matosichrvoje/matosic-macropad-pcb/matosic-macropad.kicad_sch

## KiCad design matosic-macropad.kicad_sch (2026-05-02)

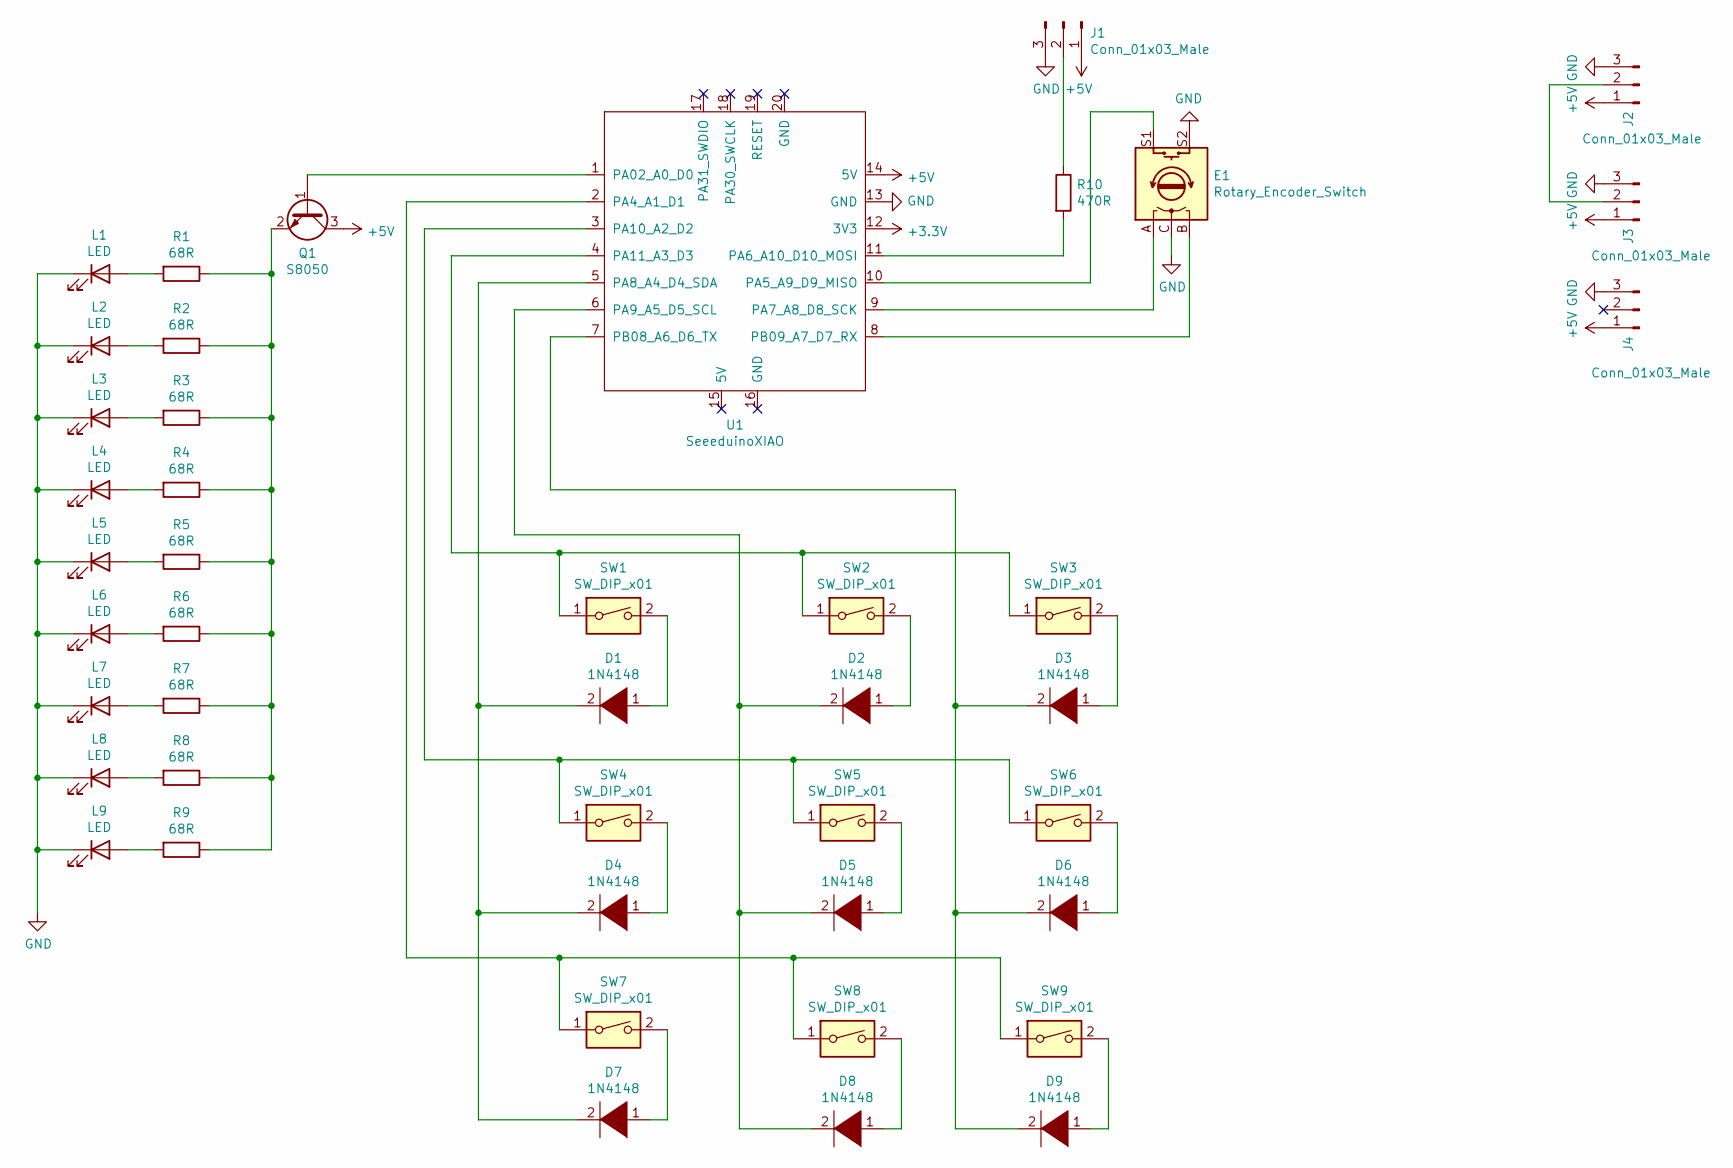
[picture p5: schematic matosic-macropad.kicad_sch]

Parts:
D1, D2, D3, D4, D5, D6, D7, D8, D9: 1N4148; D_SOD-123
E1: Rotary_Encoder_Switch; RotaryEncoder_Alps_EC11E-Switch_Vertical_H20mm
J1, J2, J3, J4: Conn_01x03_Male; LedConnector_1x03_P2.54mm
L1, L2, L3, L4, L5, L6, L7, L8, L9: LED; LED_1206_3216Metric
Q1: S8050; SOT-23
R1, R2, R3, R4, R5, R6, R7, R8, R9: 68R; R_0603_HandSoldering
R10: 470R; R_0603_HandSoldering
SW1, SW2, SW3, SW4, SW5, SW6, SW7, SW8, SW9: SW_DIP_x01; Kailh_socket_MX
U1: SeeeduinoXIAO; Seeeduino XIAO-MOUDLE14P-2.54-21X17.8MM

Connections:
+3.3V: U1.12 (3V3)
+5V: J1.1, J2.1, J3.1, J4.1, Q1.3 (C), U1.14 (5V)
GND: E1.C, E1.S2, J1.3, J2.3, J3.3, J4.3, L1.1 (K), L2.1 (K), L3.1 (K), L4.1 (K), L5.1 (K), L6.1 (K), L7.1 (K), L8.1 (K), L9.1 (K), U1.13 (GND)
unnamed: D1.1 (K), SW1.2
unnamed: D1.2 (A), D4.2 (A), D7.2 (A), U1.5 (PA8_A4_D4_SDA)
unnamed: D2.1 (K), SW2.2
unnamed: D2.2 (A), D5.2 (A), D8.2 (A), U1.6 (PA9_A5_D5_SCL)
unnamed: D3.1 (K), SW3.2
unnamed: D3.2 (A), D6.2 (A), D9.2 (A), U1.7 (PB08_A6_D6_TX)
unnamed: D4.1 (K), SW4.2
unnamed: D5.1 (K), SW5.2
unnamed: D6.1 (K), SW6.2
unnamed: D7.1 (K), SW7.2
unnamed: D8.1 (K), SW8.2
unnamed: D9.1 (K), SW9.2
unnamed: E1.A, U1.9 (PA7_A8_D8_SCK)
unnamed: E1.B, U1.8 (PB09_A7_D7_RX)
unnamed: E1.S1, U1.10 (PA5_A9_D9_MISO)
unnamed: J1.2, R10.1
unnamed: J2.2, J3.2
unnamed: L1.2 (A), R1.2
unnamed: L2.2 (A), R2.2
unnamed: L3.2 (A), R3.2
unnamed: L4.2 (A), R4.2
unnamed: L5.2 (A), R5.2
unnamed: L6.2 (A), R6.2
unnamed: L7.2 (A), R7.2
unnamed: L8.2 (A), R8.2
unnamed: L9.2 (A), R9.2
unnamed: Q1.1 (B), U1.1 (PA02_A0_D0)
unnamed: Q1.2 (E), R1.1, R2.1, R3.1, R4.1, R5.1, R6.1, R7.1, R8.1, R9.1
unnamed: R10.2, U1.11 (PA6_A10_D10_MOSI)
unnamed: SW1.1, SW2.1, SW3.1, U1.4 (PA11_A3_D3)
unnamed: SW4.1, SW5.1, SW6.1, U1.3 (PA10_A2_D2)
unnamed: SW7.1, SW8.1, SW9.1, U1.2 (PA4_A1_D1)
